MMMZZZZ/Syntherrupter/Documentation/Wiki/UI/Log In.md

# Login

[Back to the User Interface Reference page](README.md#readme)

The log in page restricts acces to Syntherrupter and allows different users to log in based on their password. 

## Index
* [Index](#index)
* [What you see](#what-you-see)
* [What you get](#what-you-get)
  * [Authentification](#authentification)
  * [Auto login and Default Passwords](#auto-log-in-and-default-passwords)

## What you see

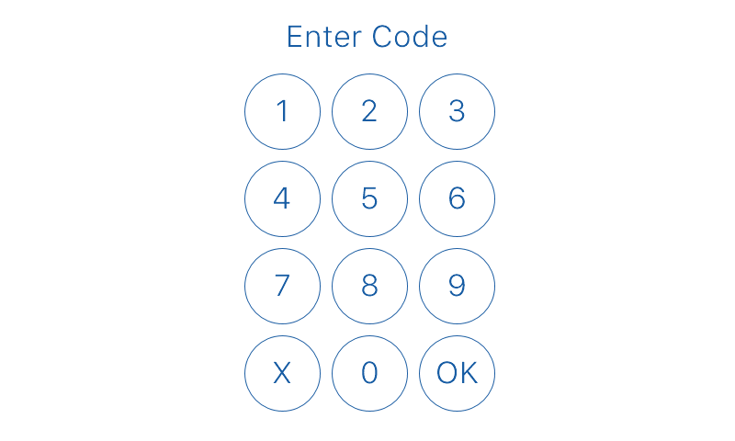
[picture p16: Documentation/Pictures/UI/Log In.png]
Log In


## What you get

### Authentification

By typing a password that matches one of the three user passwords, you'll log in with the rights of that user. You have an infinite number of attemps but a delay between each attempt. This isn't meant as a high security thing, rather to prevent "oopsies" from less experienced users you might grant access to your coil (see [User Settings](Users.md#readme) for details about the different roles). 

As you can see, the log in page only allows numbers to be entered. Thus you shouldn't set the password to anything else than a number or you won't be able to log in. 

### Auto log in and Default Passwords

This is detailed on the [User Settings](Users.md#passwords) wiki page.
