MMMZZZZ/Syntherrupter/Documentation/Wiki/UI/ESP-USB.md

# ESP8266<->USB Passthrough

[Back to the User Interface Reference page](README.md#readme)

This mode connects the ESP8266 RX/TX pins to the onboard USB-serial converter. Because this is done through software the baudrate is limited to "only" 512000 baud/s. Not much else to say except for what's written on the screen.

## Index
* [Index](#index)
* [What you see](#what-you-see)
* [Related Articles](#related-articles)

## What you see

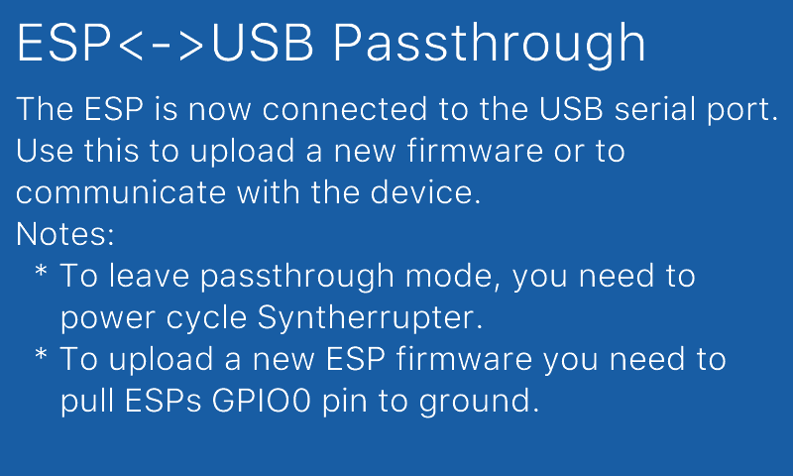
[picture p20: Documentation/Pictures/UI/ESP-USB.png]
ESP<->USB Passthrough


## Related Articles

The [Hardware Reference for the Lightsaber Receiver](/Documentation/Wiki/HW/Lightsaber%20Receiver.md#readme) includes all you need to know about connecting an ESP to the Tiva microcontroller. 

The [Lightsaber ESP8266 Setup](/Documentation/Wiki/Lightsaber%20ESP8266%20Setup.md#readme) article is your guide if you want to get those fancy lightsabers ready to use!
