MMMZZZZ/Syntherrupter/Documentation/Wiki/UI/Help and Info.md

# Help and Info

[Back to the User Interface Reference page](README.md#readme)

The Help and Info page allows you to control the "Help QR" and contains a short form of the [Credits](/README.md#Credits). If you're new to Syntherrupter and this wiki, you may want to check the [Wiki Main Page](/Documentation/Wiki/README.md#readme) or the [Getting Started article](https://github.com/MMMZZZZ/Syntherrupter/blob/dev/Documentation/Wiki/Getting%20Started.md#readme).  

## Index
* [Index](#index)
* [What you see](#what-you-see)
* [What you get](#what-you-get)
  * [Help Mode](#help-mode)
  * [Credits](#credits)

## What you see

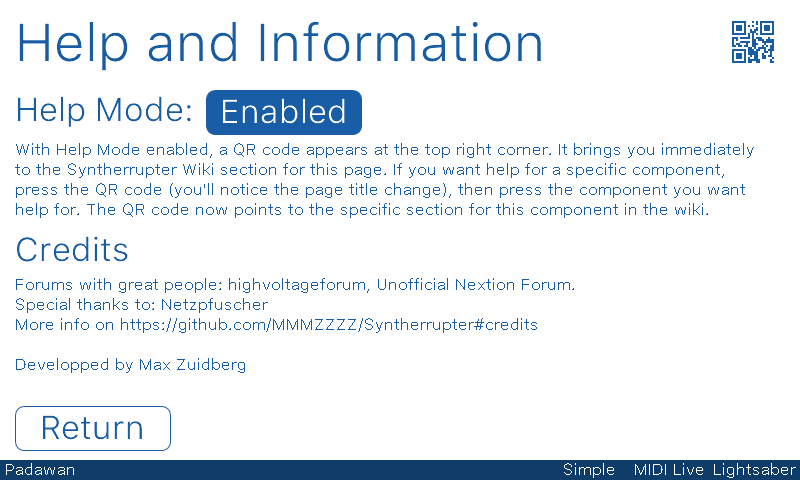
[picture p22: Documentation/Pictures/UI/Help and Info.png]
Help and Info


## What you get

### Help Mode

Mostly explained on-screen. Help mode shows a QR code at the top right (not visible when disabled), which links to the wiki article or even article section when activated. While not every wiki article offers the same level of details, the QR code works on every page. 

### Credits

As much Credits as I could fit on the screen. Full version on [Syntherrupters main page](/README.md#Credits). Oh, and a note about who I am. Hi!
