MMMZZZZ/Syntherrupter/Documentation/Wiki/UI/Error.md

# Error Page

[Back to the User Interface Reference page](README.md#readme)

Description

## Index
* [Index](#index)
* [Content](#content)

## Content

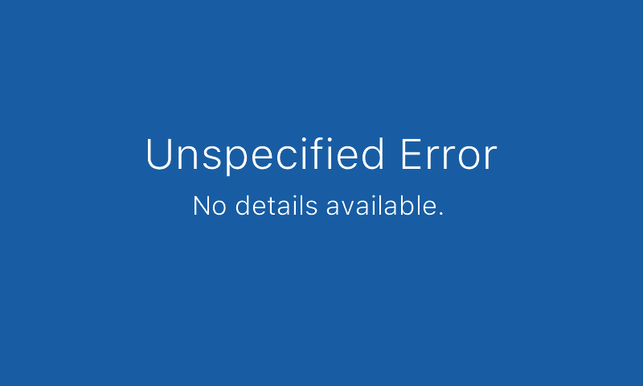
[picture p23: Documentation/Pictures/UI/Error.png]
Error Page
