MMMZZZZ/Syntherrupter/Documentation/Pictures/Syntherrupter Structure.png

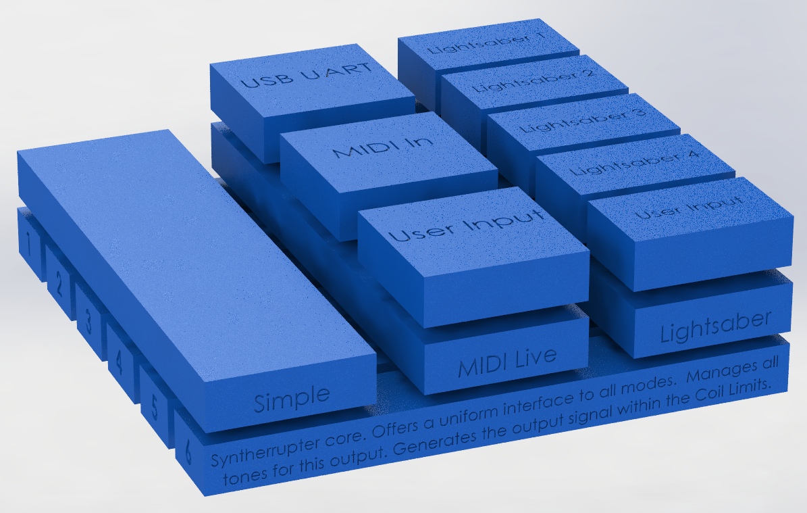
Documentation/Pictures/Syntherrupter Structure.png
