MMMZZZZ/Syntherrupter/Documentation/Pictures/Syntherrupter_Max_Back.jpeg

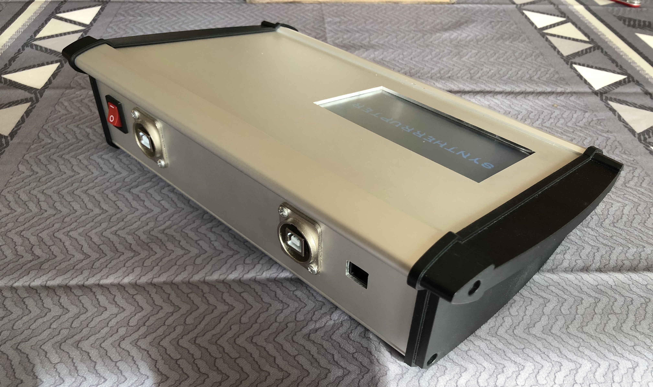
Documentation/Pictures/Syntherrupter_Max_Back.jpeg
