MMMZZZZ/Syntherrupter/Documentation/Pictures/Syntherrupter_Max_Top.jpeg

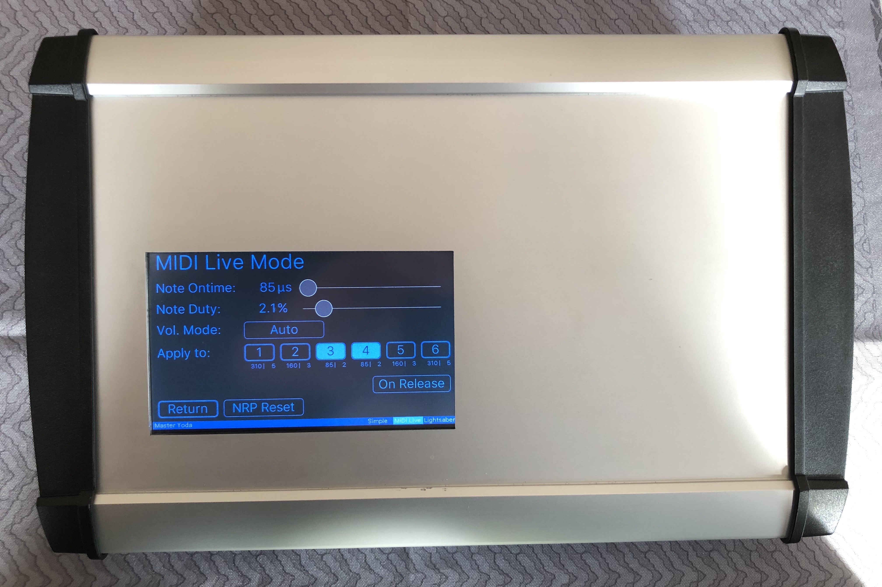
Documentation/Pictures/Syntherrupter_Max_Top.jpeg
