MMMZZZZ/Syntherrupter/Documentation/Pictures/Syntherrupter_SimonNwardUK_Top_1.jpeg

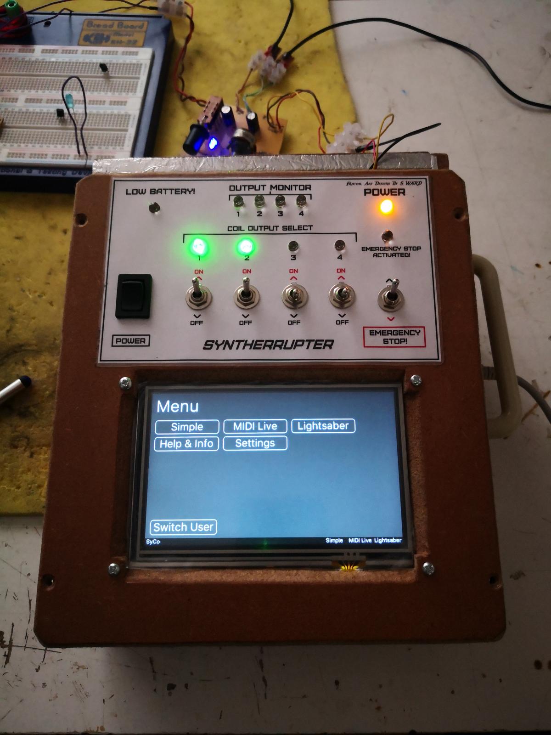
Documentation/Pictures/Syntherrupter_SimonNwardUK_Top_1.jpeg
