MMMZZZZ/Syntherrupter/Documentation/Pictures/Syntherrupter_SimonNwardUK_Top_2.jpeg

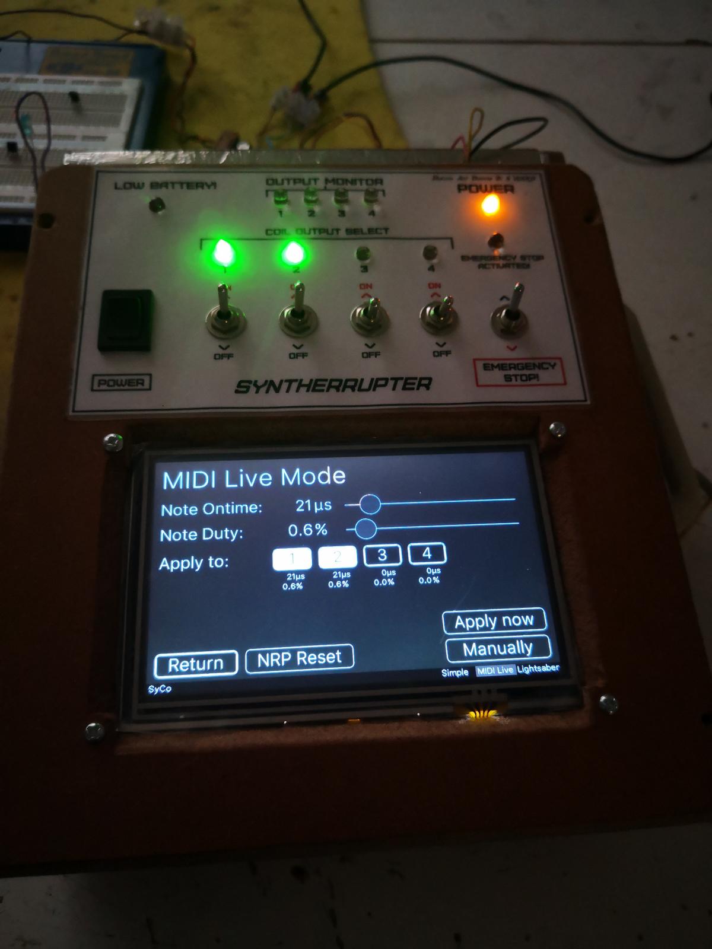
Documentation/Pictures/Syntherrupter_SimonNwardUK_Top_2.jpeg
