MMMZZZZ/Syntherrupter/Syntherrupter_Tiva/MIDI.cpp

/*
 * MIDI.cpp
 *
 *  Created on: 27.03.2020
 *      Author: Max Zuidberg
 */

#include <MIDI.h>


UART                       MIDI::usbUart;
UART                       MIDI::midiUart;
Buffer<uint8_t, 512>            MIDI::otherBuffer;
constexpr Buffer<uint8_t, 512>* MIDI::BUFFER_LIST[];
Channel                    MIDI::channels[];
NoteList                   MIDI::notelist;
uint32_t                   MIDI::notesCount = 0;
uint8_t*                   MIDI::sysexDeviceID;
SysexMsg                   MIDI::sysexMsg;
bool                       MIDI::modeRunning = false;
float                      MIDI::freqTable[128];
MIDIProgram                MIDI::programs[MAX_PROGRAMS];
float*                     MIDI::lfoFreq;
float*                     MIDI::lfoDepth;


MIDI::MIDI()
{
    // TODO Auto-generated constructor stub

}

MIDI::~MIDI()
{
    // TODO Auto-generated destructor stub
}

void MIDI::init(uint32_t usbBaudRate, void (*usbISR)(void),
                uint32_t midiUartPort, uint32_t midiUartRx,
                uint32_t midiUartTx, void(*midiISR)(void))
{
    // Static init. This stuff only needs to be done once (NOT for every instance).

    // Enable MIDI receiving over the USB UART (selectable baud rate) and a separate MIDI UART (31250 fixed baud rate).
    usbUart.init(0, usbBaudRate, usbISR, 0b00100000);
    midiUart.init(midiUartPort, midiUartRx, midiUartTx, 31250, midiISR, 0b01100000);
    usbUart.enable();
    midiUart.enable();

    MIDIProgram::setResolutionUS(effectResolutionUS);
    for (uint32_t prog = 0; prog < MAX_PROGRAMS; prog++)
    {
        programs[prog].init();
    }

    for (uint32_t note = 0; note < 128; note++)
    {
        freqTable[note] = exp2f((note - 69.0f) / 12.0f) * 440.0f;
    }

    // Store channel number in each channel object
    for (uint32_t chn = 0; chn < 16; chn++)
    {
        channels[chn].number = chn;
    }
}

void MIDI::init(uint32_t num, ToneList* tonelist)
{
    // Non-static init. This needs to be done for every instance of the class.

    this->tonelist = tonelist;
    this->coilNum  = num;
    this->coilBit  = 1 << num;

    // Correctly apply the settings already loaded by EEPROMSettings
    setMaxVoices(*coilMaxVoices);
}

bool MIDI::processBuffer(uint32_t b)
{
    /*
     * Minimum MIDI data processing.
     *
     * Returns if the parsed data requires immediate processing or not.
     * If so, the serial buffers shouldn't be processed any further until
     * all of the data parsed so far has indeed been used.
     */
    bool urgentData = false;

    /*
     * It would probably be better to have a child class of the ByteBuffer
     * class which does the buffer processing. But for now this does the
     * job, too.
     * It makes sure that the processing of the buffers is not mixed together.
     *
     */
    static uint32_t midiStatusAll[BUFFER_COUNT]{0};
    static uint32_t dataBytesAll[BUFFER_COUNT]{0};
    static uint32_t channelAll[BUFFER_COUNT]{0};
    static uint8_t  c1All[BUFFER_COUNT]{0};

    uint32_t& midiStatus = midiStatusAll[b];
    uint32_t& dataBytes  = dataBytesAll[b];
    uint32_t& channel    = channelAll[b];
    uint8_t&  c1         = c1All[b];

    auto* buffer = BUFFER_LIST[b];

    c1 = buffer->read();

    if (c1 & 0b10000000) // The first byte of a MIDI Command starts with a 1. Following bytes start with a 0.
    {
        if (0xf8 <= c1)
        {
            // System real time messages do not affect the running status.
        }
        else
        {
            // Lower 4 bits are channel.
            channel = c1 & 0x0f;

            // Save running status
            midiStatus = c1;
        }
        dataBytes = 0;
    }
    else
    {
        dataBytes++;
    }

    switch ((midiStatus) & 0xf0)
    {
        case 0x80: // Note off
        {
            if (dataBytes == 1)
            {
                Note* note = channels[channel].getNote(c1);
                if (note)
                {
                    note->velocity = 0;
                    note->changed  = true;
                    channels[channel].notesChanged = true;
                }
            }
            else if (dataBytes == 2)
            {
                // End of command, reset dataBytes counter
                dataBytes = 0;
            }
            break;
        }
        case 0x90: // Note on
        {
            static Note*    noteAll[BUFFER_COUNT]{0};
            static uint8_t  numberAll[BUFFER_COUNT]{0};
            Note*&   note   = noteAll[b];
            uint8_t& number = numberAll[b];
            if (dataBytes == 1)
            {
                number = c1;
            }
            else if (dataBytes == 2)
            {
                // End of command, reset dataBytes counter
                dataBytes = 0;

                note = channels[channel].getNote(number);
                if (c1) // Note has a velocity
                {
                    if (!note)
                    {
                        note = notelist.addNote();
                        note->afterTouch     = 0;
                        note->rawVolume      = 0.0f;
                        note->envelopeVolume = 0.0f;
                        note->finishedVolume = 0.0f;
                        note->panChanged = (1 << COIL_COUNT) - 1;
                        channels[channel].addNote(note);
                    }
                    else
                    {
                        notelist.moveToEnd(note);
                    }
                    note->number         = number;
                    note->velocity       = c1;
                    note->envelopeStep   = 0;
                    note->effectTimeUS = 0.0f;
                    note->changed        = true;
                    channels[channel].notesChanged = true;
                }
                else if (note) // Note has no velocity = note off. Code copy pasted from note off command.
                {
                    note->velocity = 0;
                    note->changed  = true;
                    channels[channel].notesChanged = true;
                }
            }
            break;
        }
        case 0xA0: // Polyphonic Aftertouch
        {
            static Note* noteAll[BUFFER_COUNT]{0};
            Note*& note = noteAll[b];
            if (dataBytes == 1)
            {
                note = notelist.getNote(channel, c1);
            }
            else if (dataBytes == 2 && note)
            {
                // End of command, reset dataBytes counter
                dataBytes = 0;

                note->afterTouch = c1;
                note->changed = true;
                channels[channel].notesChanged = true;
            }
            break;
        }
        case 0xB0: // Control Change / Channel Mode
        {
            static uint32_t controllerAll[BUFFER_COUNT]{128};
            uint32_t& controller = controllerAll[b];
            if (dataBytes == 1)
            {
                controller = c1;
            }
            else if (dataBytes == 2)
            {
                // End of command, reset dataBytes counter
                dataBytes = 0;

                switch (controller)
                {
                    default:
                        break;
                    case 0x01: // Modulation Wheel
                        channels[channel].modulation = c1 / 127.0f;
                        channels[channel].controllersChanged = true;
                        break;
                    case 0x02: // Breath Controller

                        break;
                    case 0x07: // Channel Volume
                        channels[channel].volume = c1 / 127.0f;
                        // channels[channel].controllersChanged = true;
                        break;
                    case 0x0A: // Pan
                        channels[channel].pan = c1 / 127.0f;
                        channels[channel].controllersChanged = true;
                        break;
                    case 0x0B: // Expression coarse
                        channels[channel].expression = c1 / 127.0f;
                        // channels[channel].controllersChanged = true;
                        break;
                    case 0x40: // Sustain Pedal
                        if (c1 >= 64)
                        {
                            channels[channel].sustainPedal = true;
                        }
                        else
                        {
                            channels[channel].sustainPedal = false;
                            // Pedal lifts can be very short but must be
                            // caught under all circumstances
                            urgentData = true;
                        }
                        channels[channel].controllersChanged = true;
                        break;
                    case 0x43: // Damper Pedal
                        if (c1 >= 64)
                        {
                            channels[channel].damperPedal = true;
                        }
                        else
                        {
                            channels[channel].damperPedal = false;
                        }
                        channels[channel].controllersChanged = true;
                        break;
                    case 0x62: // Non Registered Parameter Number, fine
                        channels[channel].NRPN &= 0xff00;
                        channels[channel].NRPN += c1;

                        // Can't receive RP and NRP data at the same time.
                        channels[channel].RPN   = 0x7f7f;
                        break;
                    case 0x63: // Non Registered Parameter Number, coarse
                        channels[channel].NRPN &= 0x00ff;
                        channels[channel].NRPN += (c1 << 8);

                        // Can't receive RP and NRP data at the same time.
                        channels[channel].RPN   = 0x7f7f;
                        break;
                    case 0x64: // Registered Parameter Number, fine
                        channels[channel].RPN &= 0xff00;
                        channels[channel].RPN += c1;

                        // Can't receive RP and NRP data at the same time.
                        channels[channel].NRPN = 0x7f7f;
                        break;
                    case 0x65: // Registered Parameter Number, coarse
                        channels[channel].RPN &= 0x00ff;
                        channels[channel].RPN += (c1 << 8);

                        // Can't receive RP and NRP data at the same time.
                        channels[channel].NRPN = 0x7f7f;
                        break;
                    case 0x06: // (N)RPN Data Entry, coase
                    {
                        bool previousState = channels[channel].controllersChanged;
                        channels[channel].controllersChanged = true;

                        // Registered Parameter
                        if (channels[channel].RPN == 0) // Pitch bend range
                        {
                            /*
                             * Pitch bend range is a 7+7bit value, where the upper 7 bit correspond to
                             * 0..127 semitones, whereas the lower 7bit correspond to 0..127 cents.
                             *
                             * For efficiency purposes, the scaling factor for the pitch bend command
                             * (+/-8192 => +/-1) is also included. As such only one division has to
                             * occur here, instead of one division for every pitch bend change.
                             */
                            channels[channel].pitchBendRangeCoarse = c1;
                            channels[channel].pitchBendRange  =   channels[channel].pitchBendRangeCoarse
                                                                 + channels[channel].pitchBendRangeFine / 100.0f;
                            channels[channel].pitchBendRange /= 8192.0f;
                        }
                        else if (channels[channel].RPN == 1) // Fine tuning
                        {
                            /*
                             * Fine tuning is a 14 bit value (0..16383) mapped to -1.0f..1.0f semitones
                             * Coarse tuning is a 7 bit value (0..127) shifted to -64..63 semitones
                             */
                            channels[channel].fineTuningCoarse = c1;
                            channels[channel].tuning = ((channels[channel].fineTuningCoarse << 7)
                                                        + channels[channel].fineTuningFine) - 8192.0f;
                            channels[channel].tuning /= 8192.0f;
                            channels[channel].tuning += channels[channel].coarseTuning;
                        }
                        else if (channels[channel].RPN == 2) // Coarse tuning
                        {
                            /*
                             * Fine tuning is a 14 bit value (0..16383) mapped to -1.0f..1.0f semitones
                             * Coarse tuning is a 7 bit value (0..127) shifted to -64..63 semitones
                             */
                            channels[channel].coarseTuning = c1 - 64.0f;
                            channels[channel].tuning = ((channels[channel].fineTuningCoarse << 7)
                                                        + channels[channel].fineTuningFine) - 8192.0f;
                            channels[channel].tuning /= 8192.0f;
                            channels[channel].tuning += channels[channel].coarseTuning;
                        }
                        // Non-Registered Parameter
                        else if (channels[channel].NRPN == (42 << 8) + 1) // Note pan mode - source range upper limit
                        {
                            channels[channel].notePanSourceRangeHigh = c1;
                        }
                        else if (channels[channel].NRPN == (42 << 8) + 2) // Note pan mode - target range upper limit
                        {
                            channels[channel].notePanTargetRangeHigh = c1 / 127.0f;
                        }
                        else
                        {
                            channels[channel].controllersChanged = previousState;
                        }
                        break;
                    }
                    case 0x26: // (N)RPN Data Entry, fine
                    {
                        bool previousState = channels[channel].controllersChanged;
                        channels[channel].controllersChanged = true;

                        if (channels[channel].RPN == 0) // Pitch bend range
                        {
                            /*
                             * Pitch bend range is a 7+7bit value, where the upper 7 bit correspond to
                             * 0..127 semitones, whereas the lower 7bit correspond to 0..127 cents.
                             *
                             * For efficiency purposes, the scaling factor for the pitch bend command
                             * (+/-8192 => +/-1) is also included. As such only one division has to
                             * occur here, instead of one division for every pitch bend change.
                             */
                            channels[channel].pitchBendRangeFine = c1;
                            channels[channel].pitchBendRange  =   channels[channel].pitchBendRangeCoarse
                                                                 + channels[channel].pitchBendRangeFine / 100.0f;
                            channels[channel].pitchBendRange /= 8192.0f;
                        }
                        else if (channels[channel].RPN == 1) // Fine tuning
                        {
                            /*
                             * Fine tuning is a 14 bit value (0..16383) mapped to -1.0f..1.0f semitones
                             * Coarse tuning is a 7 bit value (0..127) shifted to -64..63 semitones
                             */
                            channels[channel].fineTuningFine = c1;
                            channels[channel].tuning = ((channels[channel].fineTuningCoarse << 7)
                                                        + channels[channel].fineTuningFine) - 8192.0f;
                            channels[channel].tuning /= 8192.0f;
                            channels[channel].tuning += channels[channel].coarseTuning;
                        }
                        // Non-Registered Parameter
                        else if (channels[channel].NRPN == (42 << 8) + 0) // Note pan mode - enable/disable
                        {
                            channels[channel].notePanMode = c1;
                        }
                        else if (channels[channel].NRPN == (42 << 8) + 1) // Note pan mode - source range lower limit
                        {
                            channels[channel].notePanSourceRangeLow = c1;
                        }
                        else if (channels[channel].NRPN == (42 << 8) + 2) // Note pan mode - target range lower limit
                        {
                            channels[channel].notePanTargetRangeLow = c1 / 127.0f;
                        }
                        else
                        {
                            channels[channel].controllersChanged = previousState;
                        }
                        break;
                    }
                    case 0x78: // All Sounds off
                    {
                        Note* note = channels[channel].firstNote;
                        while (note != 0)
                        {
                            Note* nextNote = note->nextChnNote;
                            note->number = 128;
                            // Note used to be removed from the notelist here but this is now
                            // handled by updateToneList which removes the associated tones.
                            // takes one more main loop iteration but is much less convoluted.
                            // The following flag is required for MIDI::process to set the right
                            // flags for MIDI::updateToneList to update the tones.
                            channels[channel].controllersChanged = true;
                            note = nextNote;
                        }
                        break;
                    }
                    case 0x79: // Reset all Controllers
                        channels[channel].resetControllers();
                        break;
                    case 0x7B: // All Notes off
                    {
                        Note* note = channels[channel].firstNote;
                        while (note != 0)
                        {
                            note->envelopeStep = MIDIProgram::DATA_POINTS - 1;
                            note = note->nextChnNote;
                        }
                        break;
                    }
                }
            }
            break;
        }
        case 0xE0: // Pitch Bend
        {
            static float pb{0.0f};
            if (dataBytes == 1)
            {
                pb = c1 - 8192.0f;
            }
            else if (dataBytes == 2)
            {
                // End of command, reset dataBytes counter
                dataBytes = 0;

                channels[channel].pitchBend = c1 * 128.0f + pb;
                channels[channel].controllersChanged = true;
            }
            break;
        }
        case 0xD0: // Channel Aftertouch
        {
            if (dataBytes == 1)
            {
                // End of command, reset dataBytes counter
                dataBytes = 0;

                channels[channel].channelAfterTouch = c1;
                channels[channel].controllersChanged = true;

            }
            break;
        }
        case 0xC0: // Program Change
        {
            if (dataBytes == 1)
            {
                // End of command, reset dataBytes counter
                dataBytes = 0;

                if (c1 < MAX_PROGRAMS)
                {
                    channels[channel].program = c1;
                }
                else
                {
                    channels[channel].program = 0;
                }
            }
            break;
        }
        case 0xF0: // F0: SysEx start, F7: SysEx end, F[other]: idgaf
        {
            /*
             * System messages are not channel specific. As written in the
             * comment above the lower bits encode the type of system message.
             * Hence the channel variable has a different meaning in this
             * case.
             */
            uint32_t& type = channel;

            static constexpr uint32_t SYSEX_START = 0;
            static constexpr uint32_t SYSEX_END = 7;

            static uint8_t  sysexDataAll[BUFFER_COUNT][SYSEX_MAX_SIZE]{0};
            static uint32_t sysexDataIndexAll[BUFFER_COUNT]{0};
            static bool sysexUsableAll[BUFFER_COUNT]{false};
            static uint8_t  sysexVersionAll[BUFFER_COUNT]{0};

            uint8_t (&sysexData)[SYSEX_MAX_SIZE] = sysexDataAll[b];
            uint32_t &sysexDataIndex = sysexDataIndexAll[b];
            bool &sysexUsable = sysexUsableAll[b];
            uint8_t &sysexVersion = sysexVersionAll[b];

            if (dataBytes == 1)
            {
                // new sysex command, reset usable state and data index.
                sysexUsable = true;
                sysexDataIndex = 0;
            }
            else if (sysexUsable)
            {
                if (type == SYSEX_START)
                {
                    switch (dataBytes)
                    {
                        case 1: // Vendor ID. Only 2 byte IDs are accepted by Syntherrupter
                            if (c1 != 0)
                            {
                                // 1-byte ID, nothing we can support.
                                sysexUsable = false;
                            }
                            break;
                        case 2: // [Assuming a 2 byte ID] MSB of the DMID
                            /*
                             * Only Syntherrupter messages are supported, meaning the DMID must equal 0x2605
                             */
                            if (c1 != 0x26)
                            {
                                sysexUsable = false;
                            }
                            break;
                        case 3: // LSB of the DMID
                            if (c1 != 0x05)
                            {
                                sysexUsable = false;
                            }
                            break;
                        case 4: // Message Protocol Version
                            sysexVersion = c1;
                            if (sysexVersion != SYSEX_PROTOCOL_VERSION)
                            {
                                sysexUsable = false;
                            }
                            break;
                        case 5: // Device ID
                            if (c1 != *sysexDeviceID && c1 != 127)
                            {
                                // Only reply to messages directed to this
                                // device. 127 = broadcast.
                                sysexUsable = false;
                            }
                            break;
                        default: // in all other cases it are data bytes
                            if (sysexDataIndex < SYSEX_MAX_SIZE)
                            {
                                sysexData[sysexDataIndex++] = c1;
                            }
                            break;
                    }
                }
                else if (type == SYSEX_END)
                {

                    /*
                     * Sysex message completed, process data bytes.
                     * Basic format: n address bytes, m data bytes.
                     * n, m determined based on message length l:
                     *  l | n |   m
                     * ---+---+-----
                     *   2| 1 |   1
                     *   3| 1 |   2
                     *   4| 2 |   2
                     *   5| 1 |   4
                     *   6| 2 |   4
                     *   7| 2 |   5
                     *   8| 4 |   4
                     *   9| 4 |   5
                     *
                     * Data is transmitted LSB first.
                     *
                     * Currently no support for strings or message lengths outside
                     * [2,9].
                     */
                    static constexpr uint32_t BYTE_COUNT[10][2] = {
                        {0, 0}, // garbage
                        {0, 0}, // garbage
                        {1, 1},
                        {1, 2},
                        {2, 2},
                        {1, 4},
                        {2, 4},
                        {2, 5},
                        {4, 4},
                        {4, 5},
                    };

                    if (sysexDataIndex >= 2 && sysexDataIndex <= 9)
                    {
                        uint32_t number = 0;
                        uint32_t targetLSB = 0;
                        uint32_t targetMSB = 0;
                        int32_t sysexVal = 0;

                        switch (BYTE_COUNT[sysexDataIndex][0])
                        {
                            case 4:
                                targetMSB = sysexData[3];
                            case 3:
                                targetLSB = sysexData[2];
                            case 2:
                                number += sysexData[1] << 8;
                            case 1:
                                number += sysexData[0];
                                break;
                        }

                        for (uint32_t i = 0; i < BYTE_COUNT[sysexDataIndex][1]; i++)
                        {
                            sysexVal += sysexData[BYTE_COUNT[sysexDataIndex][0] + i] << (7 * i);
                        }

                        sysexMsg.version   = sysexVersion;
                        sysexMsg.number    = number;
                        sysexMsg.targetLSB = targetLSB;
                        sysexMsg.targetMSB = targetMSB;
                        sysexMsg.value.i32 = sysexVal;
                        sysexMsg.newMsg    = 2;

                        // This is not nice, I know.
                        if (buffer == &midiUart.rxBuffer)
                        {
                            sysexMsg.origin = &midiUart;
                        }
                        else
                        {
                            // Use the USB UART as default
                            sysexMsg.origin = &usbUart;
                        }

                        // Make sure the SysEx Message will be processed before
                        // it'll be overwritten by a new one.
                        urgentData = true;
                    }
                }
            }
        }
    }

    return urgentData;
}

void MIDI::setRunning(bool run)
{
    if (run != modeRunning)
    {
        modeRunning = run;
        if (modeRunning)
        {
            for (uint32_t channel = 0; channel < 16; channel++)
            {
                channels[channel].resetControllers();
            }
        }
        else
        {
            modeRunning = false;
            notelist.removeAllNotes();
        }
    }
}

void MIDI::setVolSettingsPerm(float ontimeUSMax, float dutyPermMax)
{
    // duty in promille
    setVolSettings(ontimeUSMax, dutyPermMax / 1000.0f);
}
void MIDI::setVolSettings(float ontimeUSMax, float dutyMax)
{
    singleNoteMaxOntimeUS = ontimeUSMax;
    singleNoteMaxDuty     = dutyMax;

    // Prevent divide by 0.
    if (ontimeUSMax < 1.0f)
    {
        ontimeUSMax = 1.0f;
    }

    // Determine crossover note at which abs. and rel. mode would have equal frequency.
    absFreq = dutyMax / ontimeUSMax * 1e6f;

    coilChange = true;
}

void MIDI::setChannels(uint32_t chns)
{
    activeChannels = chns;
    for (uint32_t i = 0; i < 16; i++)
    {
        if (chns & (1 << i))
        {
            channels[i].coils |=  coilBit;
        }
        else
        {
            channels[i].coils &= ~coilBit;
        }
    }

    coilChange = true;
}

void MIDI::setPan(float pan)
{
    if (pan >= 0.0f && pan <= 1.0f)
    {
        coilPan = pan;
    }
    else
    {
        coilPan = -1.0f;
    }
    coilPanChanged = true;
}

void MIDI::setPanReach(float reach)
{
    if (reach >= 0.0f && reach <= 1.0f)
    {
        inversPanReach = 1.0f / reach;
    }
    else
    {
        // only needs to be >>128.0f
        inversPanReach = 1024.0f;
    }
    coilPanChanged = true;
}

void MIDI::setMaxVoices(uint32_t maxVoices)
{
    if (maxVoices > TONE_COUNT_MIDI)
    {
        maxVoices = TONE_COUNT_MIDI;
    }
    *coilMaxVoices = maxVoices;
    coilChange = true;
}

void MIDI::resetNRPs(uint32_t chns)
{
    /*
     *  The bits in chns indicate which channels shall reset their NRPs.
     *  A value equal or higher than 2^16-1 causes a reset on all channels.
     *  Default value is 0xffff (reset on all channels).
     */

    if (chns > 0xffff)
    {
        chns = 0xffff;
    }
    for (uint32_t i = 0; i < 16; i++)
    {
        if (chns & (1 << i))
        {
            channels[i].resetNRPs();
            channels[i].controllersChanged = true;
        }
    }
}

void MIDI::process()
{
    // Process all data that's in the buffer.
    bool newData = false;
    bool forceUpdate = false;
    for (uint32_t bufferNum = 0; bufferNum < BUFFER_COUNT; bufferNum++)
    {
        while (BUFFER_LIST[bufferNum]->level() && !forceUpdate)
        {
            newData = true;
            forceUpdate = processBuffer(bufferNum);
        }
        if (forceUpdate)
        {
            break;
        }
    }

    if (modeRunning)
    {
        if (newData)
        {
            for (uint32_t channelNum = 0; channelNum < 16; channelNum++)
            {
                Channel* channel = &(channels[channelNum]);

                if (channel->notesChanged || channel->controllersChanged)
                {
                    Note* note = channel->firstNote;
                    while (note != 0)
                    {
                        if (channel->controllersChanged || note->changed)
                        {
                            note->changed = false;
                            note->toneChanged = (1 << COIL_COUNT) - 1;

                            if (note->number <= 127 && (note->velocity || channel->sustainPedal))
                            {
                                note->pitch =   float(note->number)
                                              + channel->pitchBend * channel->pitchBendRange
                                              + channel->tuning;
                                note->frequency = getFreq(note->pitch);
                                note->periodUS = 1e6f / note->frequency;

                                // Determine MIDI volume, including all effects that are not time-dependant.
                                if (note->velocity)
                                {
                                    note->rawVolume = note->velocity / 127.0f;
                                    /*
                                     * Branchless version of:
                                     * if (channel->damperPedal)
                                     * {
                                     *     note->rawVolume *= 0.6f;
                                     * }
                                     */
                                    note->rawVolume *= (1 - channel->damperPedal * 0.4f);
                                }
                            }
                            else if (!channel->sustainPedal)
                            {
                                note->envelopeStep = MIDIProgram::DATA_POINTS - 1;
                            }
                        }
                        note = note->nextChnNote;
                    }

                    channel->notePanDataUpdate();
                    note = channel->firstNote;
                    while (note != 0)
                    {
                        float oldPan = note->pan;
                        if (channel->notePanMode != Channel::NOTE_PAN_OFF)
                        {
                            /*
                             * In this mode a note number determines the pan position of the note.
                             * This is done with a mapping. A source range, covering any part of
                             * the [0..127] note number range, will be mapped to a target range,
                             * covering any part of the [0..1] pan position range.
                             */
                            float notePanInput = 0.0f;
                            if (channel->notePanMode == Channel::NOTE_PAN_INDIVIDUAL)
                            {
                                notePanInput = note->pitch;
                            }
                            else
                            {
                                notePanInput = channel->notePan;
                            }
                            if (notePanInput <= channel->notePanSourceRangeLow)
                            {
                                note->pan = channel->notePanTargetRangeLow;
                            }
                            else if (notePanInput >= channel->notePanSourceRangeHigh)
                            {
                                note->pan = channel->notePanTargetRangeHigh;
                            }
                            else
                            {
                                note->pan =   (notePanInput - channel->notePanSourceRangeLow)
                                            * (channel->notePanTargetRangeHigh - channel->notePanTargetRangeLow)
                                            / (channel->notePanSourceRangeHigh - channel->notePanSourceRangeLow)
                                            +  channel->notePanTargetRangeLow;
                            }
                        }
                        else
                        {
                            note->pan = channel->pan;
                        }

                        if (note->pan != oldPan)
                        {
                            note->panChanged = (1 << COIL_COUNT) - 1;
                        }

                        note = note->nextChnNote;
                    }
                    channel->controllersChanged = false;
                    channel->notesChanged       = false;
                }
            }
        }

        Note* note = notelist.firstNote;
        while (note != notelist.newNote)
        {
            updateEffects(note);
            note = note->nextNote;
        }
    }
}

void MIDI::updateEffects(Note* note)
{
    // Needed for envelopes
    float currentTime = System::getSystemTimeUS();
    if (note->effectTimeUS == 0.0f)
    {
        note->effectTimeUS = currentTime;
    }
    else
    {
        float timeDiffUS = currentTime - note->effectTimeUS;
        if (timeDiffUS >= effectResolutionUS)
        {
            note->effectTimeUS = currentTime;
            MIDIProgram* program = &(programs[note->channel->program]);
            if (!program->setEnvelopeAmp(&(note->envelopeStep), &(note->envelopeVolume)))
            {
                // Note ended.
                note->number = 128;
                note->toneChanged = (1 << COIL_COUNT) - 1;
            }
            else
            {

                // After calculation of envelope, add other effects like modulation
                float finishedVolume =   note->rawVolume
                                       * note->channel->volume
                                       * note->channel->expression
                                       * note->envelopeVolume
                                       * (1.0f - getLFOVal(note->channel));
                if (finishedVolume != note->finishedVolume)
                {
                    note->toneChanged = (1 << COIL_COUNT) - 1;
                    note->finishedVolume = finishedVolume;
                }
            }
        }
        if (timeDiffUS < 0.0f)
        {
            // Time overflowed
            note->effectTimeUS = currentTime;
        }
    }
}

void MIDI::updateToneList()
{
    uint32_t firstAvailableTone = TONE_COUNT_MIDI;
    Note* note = notelist.newNote->prevNote;
    int32_t voicesLeft = *coilMaxVoices;
    int32_t remainingNotes = notelist.activeNotes;
    while (remainingNotes--)
    {
        // Go backwards from the most recent to the oldest (firstNote)
        // The next note of the loop needs to be stored at the beginning
        // since the note might get deleted during the loop.
        Note* nextNote = note->prevNote;
        if ((note->toneChanged & coilBit) || coilChange || !voicesLeft)
        {
            note->toneChanged &= ~coilBit;

            uint32_t* assignedToneNum = &(note->assignedToneNums[coilNum]);

            if (note->isDead())
            {
                // Only remove note if tone has been removed.
                // Since tones are always strictly added in order, there's
                // no need to always check all of the coils. If the current one
                // has already been removed, then we're in the iteration after
                // *all* tones have been removed.
                if (*assignedToneNum == TONE_COUNT_MIDI)
                {
                    // Does not handle the associated tone from tonelists
                    notelist.removeNote(note);
                }
                else
                {
                    // Set ontime to zero, making the tone inactive.
                    // Note: tonelist handles the check whether or not
                    // assignedToneNum is even valid (a.k.a. there is an assigned tone)
                    tonelist->updateTone<ToneList::Owner::MIDI_LIVE>(*assignedToneNum, Tone::Type::dflt, 0, 0, 0, 0);
                    firstAvailableTone = *assignedToneNum;
                    *assignedToneNum = TONE_COUNT_MIDI;
                }

                // "undo" decrement at the end of the loop since no voice
                // will actually be used.
                voicesLeft++;
            }
            else if ((note->channel->coils & coilBit) && voicesLeft)
            {
                setPanVol(note);
                float ontimeUS = note->finishedVolume * note->panVol[coilNum];
                if (note->frequency >= absFreq)
                {
                    ontimeUS *= singleNoteMaxOntimeUS;
                }
                else
                {
                    ontimeUS *= singleNoteMaxDuty * note->periodUS;
                }
                if (ontimeUS < 1.0f)
                {
                    // Set ontime to zero, making the tone inactive. 
                    // Note: tonelist handles the check whether or not
                    // assignedToneNum is even valid (a.k.a. there is an assigned tone)
                    tonelist->updateTone<ToneList::Owner::MIDI_LIVE>(*assignedToneNum, Tone::Type::dflt, 0, 0, 0, 0);
                    firstAvailableTone = *assignedToneNum;
                    *assignedToneNum = TONE_COUNT_MIDI;
                }
                else
                {
                    // Get the first free tone, potentially "reusing" one that has been freed up
                    if (*assignedToneNum >= TONE_COUNT_MIDI)
                    {
                        if (firstAvailableTone < TONE_COUNT_MIDI)
                        {
                            *assignedToneNum = firstAvailableTone;
                        }
                        else 
                        {
                            *assignedToneNum = tonelist->getFreeTone<ToneList::Owner::MIDI_LIVE>();
                        }
                    }

                    tonelist->updateTone<ToneList::Owner::MIDI_LIVE>(*assignedToneNum, Tone::Type::dflt, ontimeUS, note->periodUS, 0, 0);
                }
            }
            else
            {
                // This coil is no more listening to this channel. Remove the
                // assigned tone if there is one.
                // Or the voice limit's been reached and the note doesn't fit
                // into this output anymore.
                if (*assignedToneNum)
                {
                    tonelist->updateTone<ToneList::Owner::MIDI_LIVE>(*assignedToneNum, Tone::Type::dflt, 0, 0, 0, 0);
                    firstAvailableTone = *assignedToneNum;
                    *assignedToneNum = TONE_COUNT_MIDI;
                }
            }
        }

        note = nextNote;
        // Prevent voicesLeft from going negative.
        voicesLeft = Branchless::max(0, voicesLeft - 1);
    }
    coilChange     = false;
    coilPanChanged = false;
}
