MMMZZZZ/Syntherrupter/Syntherrupter_Tiva/MIDI.h

/*
 * MIDI.h
 *
 *  Created on: 27.03.2020
 *      Author: Max Zuidberg
 */

#ifndef MIDI_H_
#define MIDI_H_


#include <stdbool.h>
#include <stdint.h>
#include "InterrupterConfig.h"
#include "Branchless.h"
#include "System.h"
#include "Channel.h"
#include "UART.h"
#include "Buffer.h"
#include "ToneList.h"
#include "NoteList.h"
#include "MIDIProgram.h"
#include "SysexMsg.h"


class MIDI
{
public:
    MIDI();
    virtual ~MIDI();
    void init(uint32_t num, ToneList* tonelist);
    void updateToneList();
    void setVolSettingsPerm(float ontimeUSMax, float dutyMaxProm);
    void setVolSettings(float ontimeUSMax, float dutyMax);
    void setOntimeUS(float ontimeUSMax)
    {
        setVolSettings(ontimeUSMax, singleNoteMaxDuty);
    };
    void setDuty(float dutyMax)
    {
        setVolSettings(singleNoteMaxOntimeUS, dutyMax);
    };
    void setChannels(uint32_t chns);
    uint32_t getChannels()
    {
        return activeChannels;
    };
    void setPan(float pan);
    float getPan()
    {
        return coilPan;
    };
    void setPanReach(float reach);
    float getPanReach()
    {
        return 1.0f / inversPanReach;
    };
    void setPanConstVol(bool cnst)
    {
        panConstVol    = cnst;
        coilPanChanged = true;
    };
    bool getPanConstVol()
    {
        return panConstVol;
    };
    void setMaxVoices(uint32_t maxVoices);
    uint32_t getMaxVoices()
    {
        return *coilMaxVoices;
    };
    float getOntimeUS()
    {
        return singleNoteMaxOntimeUS;
    };
    float getDuty()
    {
        return singleNoteMaxDuty;
    };
    static void init(uint32_t usbBaudRate, void (*usbISR)(void),
                     uint32_t midiUartPort, uint32_t midiUartRx,
                     uint32_t midiUartTx, void (*midiISR)(void));
    static void setRunning(bool run);
    static bool getRunning()
    {
        return modeRunning;
    };
    static void resetNRPs(uint32_t chns = 0xffff);
    static void process();
    static SysexMsg getSysex()
    {
        if (sysexMsg.newMsg)
        {
            sysexMsg.newMsg--;
        }
        return sysexMsg;
    }
    static Channel channels[16];
    static UART usbUart, midiUart;
    static Buffer<uint8_t, 512> otherBuffer;
    static constexpr uint32_t MAX_PROGRAMS = 64;
    static MIDIProgram programs[MAX_PROGRAMS];
    static constexpr uint32_t SYSEX_PROTOCOL_VERSION = 1;

private:
    static bool processBuffer(uint32_t b);
    static void updateEffects(Note* note);
    static void processSysex(uint32_t sysexNum, uint32_t targetLSB, uint32_t targetMSB, int32_t sysexVal);
    void setPanVol(Note* note)
    {
        if (note->panChanged || coilPanChanged)
        {
            note->panChanged &= ~coilBit;
            // 1.01f instead of 1.0f to include the borders of the range.

            // Limit lower range to 0.0f
            note->panVol[coilNum] = Branchless::max(0.0f, 1.01f - inversPanReach * fabsf(note->pan - coilPan));

            // if panVol != 0 and panConstVol, set panVol to 1.0f
            // Detailed explanation of the reasoning below.
            float panConstant = (panConstVol && note->panVol[coilNum]);
            note->panVol[coilNum] = Branchless::max(note->panVol[coilNum], panConstant);
        }

        /*
         * panVol now ranges from 0-1. If pan stuff is for some reason disabled
         * panVol should be 1. So if condition is true == 1, set panVol to 1.
         * Effectively this is the same as max(panVol, condition). If the
         * condition is false (== 0, meaning that pan stuff *is* enabled), then
         * the panVol is in all cases >= than the condition and remains
         * unchanged. Otherwise - with the same reasoning - it'll be changed to
         * 1.0f.
         * Previous code:
         *     if (coilPan < 0.0f || note->channel->notePanMode == Channel::NOTE_PAN_OMNI)
         *     {
         *         note->panVol[coilNum] = 1.0f;
         *     }
         */
        float panDisabled = (coilPan < 0.0f || note->channel->notePanMode == Channel::NOTE_PAN_OMNI);
        note->panVol[coilNum] = Branchless::max(note->panVol[coilNum], panDisabled);
    };
    static float getLFOVal(Channel* channel)
    {
        if (channel->modulation)
        {
            /*
             * LFO_SINE = sin( 2 * Pi * f * t[us] * 1e-6 )
             *
             *       1   /  LFO_SINE + 1       ModWheelValue    \
             * val = - * | --------------- * ------------------ |
             *       2   \        2           MaxModWheelValue  /
             *
             * sine wave between 0 and 1 mapped to the desired modulation depth (50% max).
             */
            return (sinf(6.283185307179586e-6f * float(System::getSystemTimeUS()) * (*lfoFreq)) + 1) / 2.0f
                    * channel->modulation * (*lfoDepth);
        }
        else
        {
            return 0.0f;
        }
    };
    static void removeDeadNotes();
    static float getFreq(float pitch)
    {
        if (pitch <= 0.0f)
        {
            return freqTable[0];
        }
        else if (pitch >= 127.0f)
        {
            return freqTable[127];
        }
        else
        {
            uint32_t intPitch = pitch;
            float fracPitch = pitch - intPitch;
            float freq = freqTable[intPitch];
            freq += (freqTable[intPitch + 1] - freq) * fracPitch;
            return freq;
        }
    };

    static float freqTable[128];

    static constexpr uint32_t effectResolutionUS = 2000;

    static constexpr uint32_t SYSEX_MAX_SIZE = 16;
    static constexpr uint32_t    BUFFER_COUNT = 3;
    static constexpr Buffer<uint8_t, 512>* BUFFER_LIST[BUFFER_COUNT] = {&(usbUart.rxBuffer), &(midiUart.rxBuffer), &otherBuffer};
    static constexpr uint32_t MAX_NOTES_COUNT = 64;
    static NoteList notelist;
    static uint32_t notesCount;
    static uint8_t* sysexDeviceID;
    static SysexMsg sysexMsg;
    ToneList* tonelist;
    float absFreq               =  0.0f;
    float singleNoteMaxDuty     =  0.0f;
    float singleNoteMaxOntimeUS =  0.0f;
    float coilPan               = -1.0f;
    float inversPanReach        =  0.0f;
    uint8_t volMode             =  3;
    uint16_t activeChannels     =  0xffff;
    uint32_t* coilMaxVoices;
    uint32_t coilNum            =  0;
    uint8_t  coilBit            =  0;
    bool coilChange             = false;
    bool coilPanChanged         = false;
    bool panConstVol            = false;

    static bool modeRunning;
    static float* lfoFreq;
    static float* lfoDepth;

    friend class EEPROMSettings;
    friend class Effect;
};

#endif /* H_ */
