MMMZZZZ/Syntherrupter/Syntherrupter_Tiva/GUI.h

/*
 * GUI.h
 *
 *  Created on: 26.03.2020
 *      Author: Max Zuidberg
 */

#ifndef GUI_H_
#define GUI_H_


#include "stdint.h"
#include "stdbool.h"
#include "driverlib/gpio.h"
#include "InterrupterConfig.h"
#include "Branchless.h"
#include "System.h"
#include "EEPROMSettings.h"
#include "Nextion.h"
#include "Coil.h"


class GUI
{
public:
    GUI();
    virtual ~GUI();
    static void init(Nextion* nextion, uint32_t cfgStatus);
    static void syncAllSettings();
    static void update();
    static void applyOutput();
    static void setError(const char* err);
    static void showError();
    static void EEEE();
    static bool getAcceptsData()
    {
        return acceptsData;
    }
private:
    enum class Mode {
        emergency,
        idle,
        simpleEnter,
        simple,
        simpleExit,
        midiLiveEnter,
        midiLive,
        midiLiveExit,
        lightsaberEnter,
        lightsaber,
        lightsaberExit,
        userSelect,
        settings,
        settingsExit,
        nxtFWUpdate,
        espFWUpdate,
    };
    static void idle()
    {
        state = 0;
    };

    static void simpleEnter()
    {
        Simple::setRunning(true);
    };

    static void simple();
    static void simpleExit()
    {
        Simple::setRunning(false);
    };

    static void midiLiveEnter()
    {
        MIDI::setRunning(true);
    };

    static void midiLive();
    static void midiLiveExit()
    {
        // Stop MIDI operation
        MIDI::setRunning(false);
        EEE = false;
    };

    static void lightsaberEnter()
    {
        LightSaber::setRunning(true);
    }
    static void lightsaber();
    static void lightsaberExit()
    {
        LightSaber::setRunning(false);
    }

    static void userSelect();
    static void settings();
    static void settingsExit()
    {
        // Update EEPROM
        EEPROMSettings::updateAll();
    };

    static void serialPassthrough(uint32_t uartNum);

    static bool checkValue(int32_t val);

    static Nextion* nxt;

    static bool acceptsData;

    static uint32_t state;
    static uint32_t command;
    static uint32_t commandData[33]; // sized to max length of all commands.
    static Mode mode;

    static constexpr uint32_t errorLen = 20;
    static char errorTxt[errorLen];

    static bool EEE;
    static uint32_t EET;
    static uint32_t EEI;
    static constexpr uint32_t EES = 1572;
    static constexpr uint8_t EED[EES][4] = {{0, 0xbd, 0x79, 0x00}, {0, 0xbd, 0x7b, 0x00}, {1, 0xb8, 0x00, 0x00}, {0  , 0xc8, 0x0a, 0x0a}, {0, 0xb8, 0x07, 0x64}, {0, 0xbd, 0x00, 0x00}, {0, 0xcd, 0x0a, 0x0a}, {0, 0xbd, 0x07, 0x64}, {0, 0x9d, 0x35, 0x6e}, {53, 0x8d, 0x35, 0x00}, {0, 0x9d, 0x3a, 0x6e}, {19, 0x8d, 0x3a, 0x00}, {0, 0x9d, 0x3f, 0x6e}, {112, 0x8d, 0x3f, 0x00}, {0, 0x9d, 0x3e, 0x6e}, {37, 0x8d, 0x3e, 0x00}, {0, 0x9d, 0x3a, 0x6e}, {26, 0x8d, 0x3a, 0x00}, {0, 0x9d, 0x37, 0x6e}, {25, 0x8d, 0x37, 0x00}, {0, 0x9d, 0x3c, 0x6e}, {25, 0x8d, 0x3c, 0x00}, {0, 0x9d, 0x41, 0x6e}, {0, 0x9d, 0x41, 0x7f}, {56, 0x8d, 0x41, 0x00}, {0, 0x9d, 0x46, 0x7f}, {19, 0x8d, 0x46, 0x00}, {0, 0x9d, 0x4b, 0x7f}, {112, 0x8d, 0x4b, 0x00}, {0, 0x9d, 0x4a, 0x7f}, {38, 0x8d, 0x4a, 0x00}, {0, 0x9d, 0x46, 0x7f}, {26, 0x8d, 0x46, 0x00}, {0, 0x9d, 0x43, 0x7f}, {25, 0x8d, 0x43, 0x00}, {0, 0x9d, 0x48, 0x7f}, {25, 0x8d, 0x48, 0x00}, {0, 0x9d, 0x4d, 0x7f}, {131, 0x8d, 0x4d, 0x00}, {0, 0x8d, 0x41, 0x00}, {0, 0x9d, 0x41, 0x7f}, {0, 0x9d, 0x4d, 0x7f}, {18, 0x8d, 0x4d, 0x00}, {0, 0x8d, 0x41, 0x00}, {0, 0x9d, 0x44, 0x7f}, {0, 0x9d, 0x50, 0x7f}, {125, 0x8d, 0x50, 0x00}, {0, 0x8d, 0x44, 0x00}, {0, 0x98, 0x50, 0x64}, {0, 0x98, 0x50, 0x64}, {0, 0x98, 0x5c, 0x4a}, {6, 0x88, 0x5c, 0x00}, {0, 0x88, 0x50, 0x00}, {0, 0x88, 0x50, 0x00}, {0, 0x98, 0x4b, 0x64}, {0, 0x98, 0x4b, 0x64}, {0, 0x98, 0x57, 0x4a}, {5, 0x88, 0x57, 0x00}, {0, 0x88, 0x4b, 0x00}, {0, 0x88, 0x4b, 0x00}, {0, 0x98, 0x4d, 0x64}, {0, 0x98, 0x4d, 0x64}, {0, 0x9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
7, 0x00}, {0, 0x9d, 0x37, 0x64}, {0, 0x9d, 0x43, 0x7f}, {11, 0x8d, 0x43, 0x00}, {0, 0x8d, 0x37, 0x00}, {0, 0x9d, 0x37, 0x64}, {0, 0x9d, 0x43, 0x7f}, {12, 0x8d, 0x43, 0x00}, {0, 0x8d, 0x37, 0x00}, {0, 0x9d, 0x37, 0x64}, {0, 0x9d, 0x43, 0x7f}, {12, 0x8d, 0x43, 0x00}, {0, 0x8d, 0x37, 0x00}, {246, 0xb8, 0x79, 0x00}, {0, 0xb8, 0x7b, 0x00}, {0, 0xbd, 0x79, 0x00}, {0, 0xbd, 0x7b, 0x00}};
};

#endif /* GUI_H_ */
